Franzininho/badge-Aprenda-Soldar/img/02.jpg

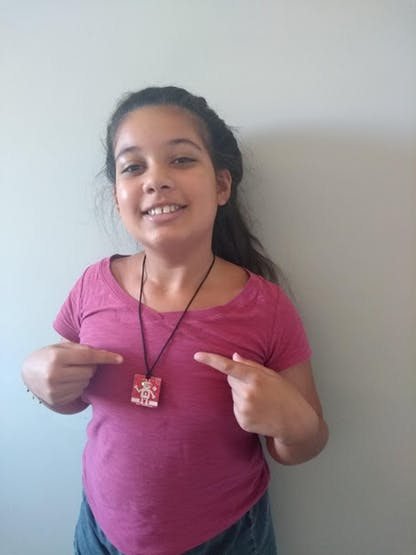
img/02.jpg
