Franzininho/badge-Aprenda-Soldar/img/01.jpg

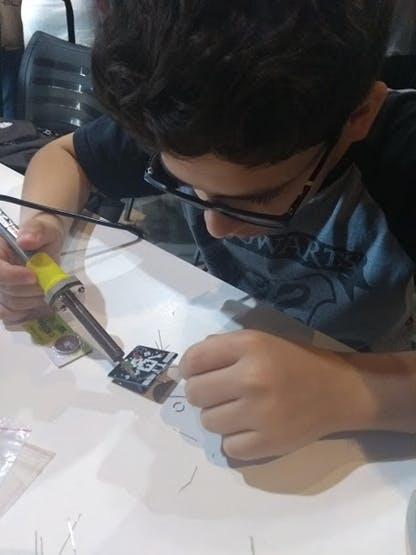
img/01.jpg
