Franzininho/badge-Aprenda-Soldar/img/03.jpg

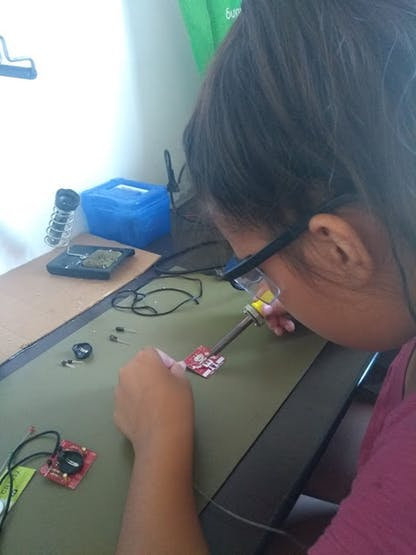
img/03.jpg
