Franzininho/badge-Aprenda-Soldar/img/04.jpg

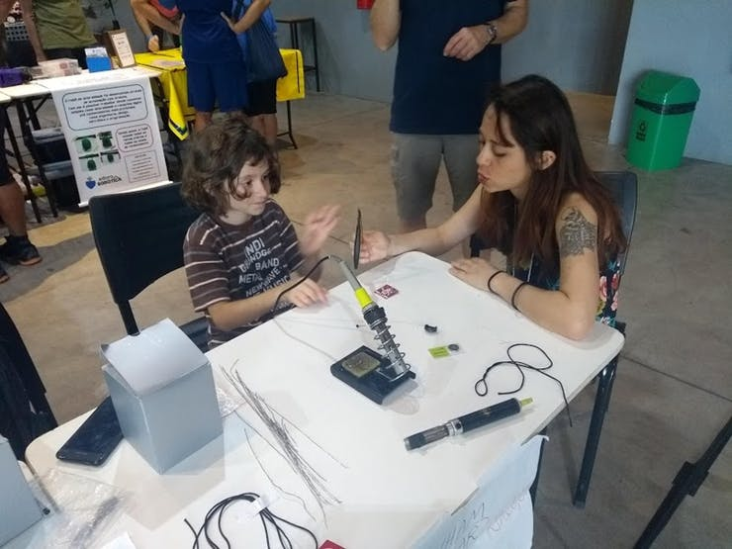
img/04.jpg
