Franzininho/badge-Aprenda-Soldar/img/06.jpg

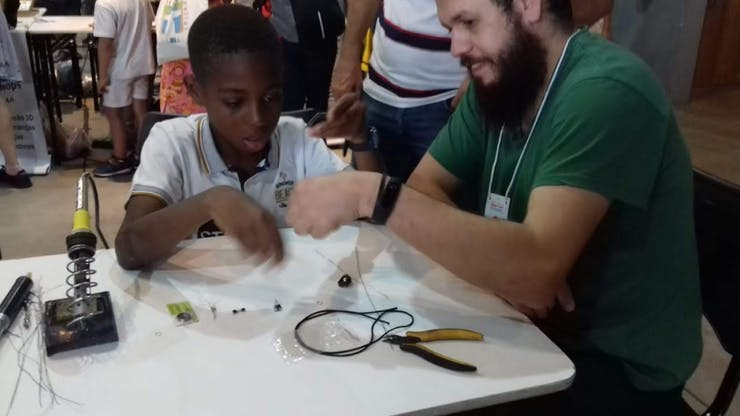
img/06.jpg
