Franzininho/badge-Aprenda-Soldar/img/07.jpeg

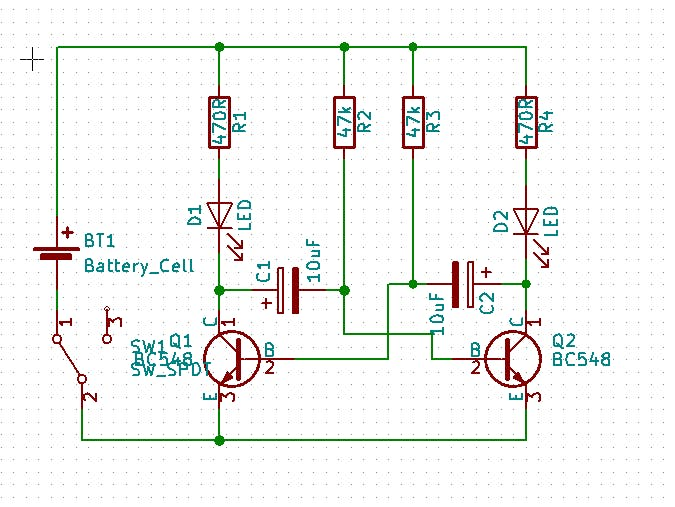
img/07.jpeg
