Franzininho/badge-Aprenda-Soldar/img/08.jpeg

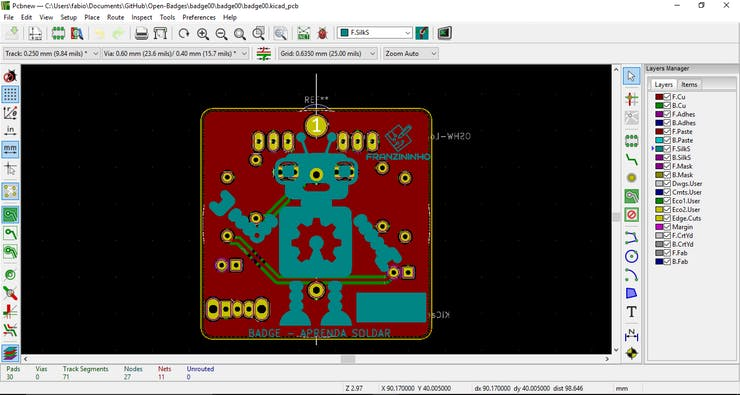
img/08.jpeg
