Franzininho/badge-Aprenda-Soldar/img/09.jpeg

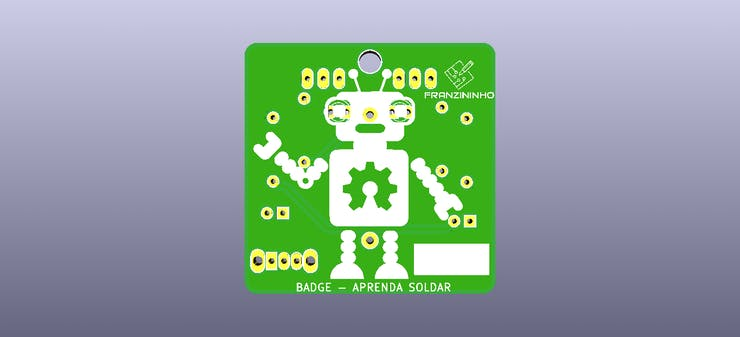
img/09.jpeg
