Franzininho/badge-Aprenda-Soldar/img/10.jpeg

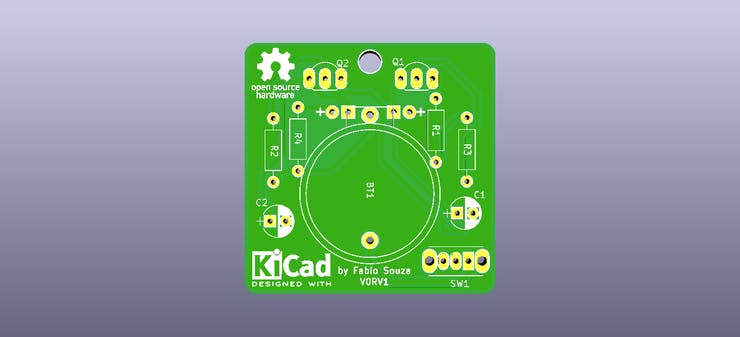
img/10.jpeg
