Franzininho/badge-Aprenda-Soldar/img/12.jpeg

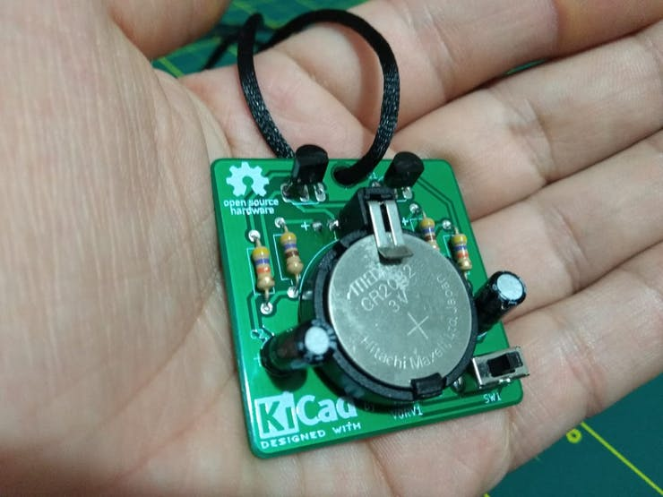
img/12.jpeg
