Franzininho/badge-Aprenda-Soldar/img/13.jpg

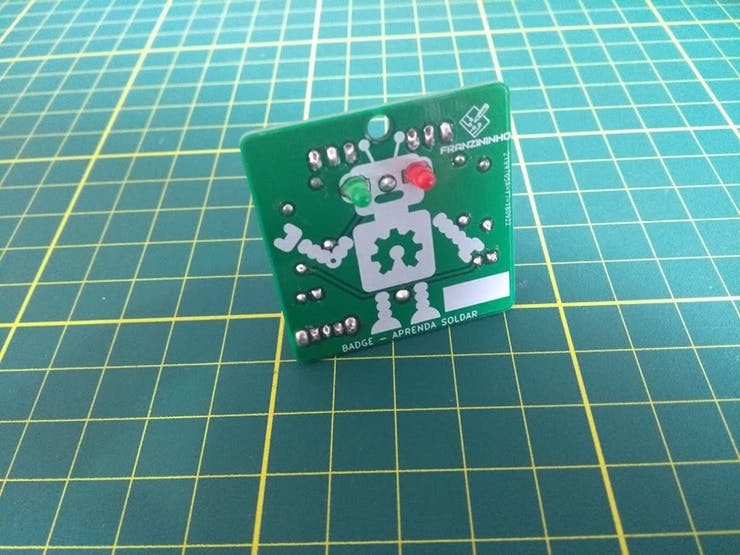
img/13.jpg
