Franzininho/badge-Aprenda-Soldar/img/14.jpeg

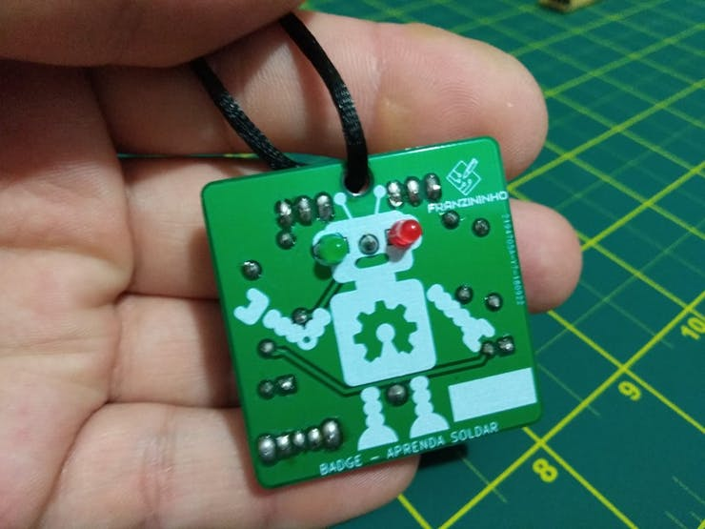
img/14.jpeg
