Franzininho/badge-Aprenda-Soldar/img/15.png

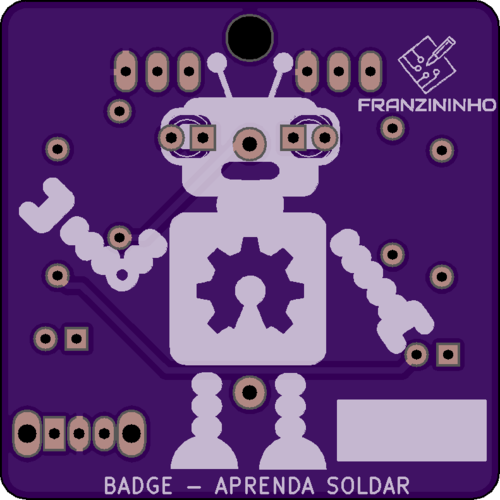
img/15.png
