Franzininho/badge-Aprenda-Soldar/img/16.png

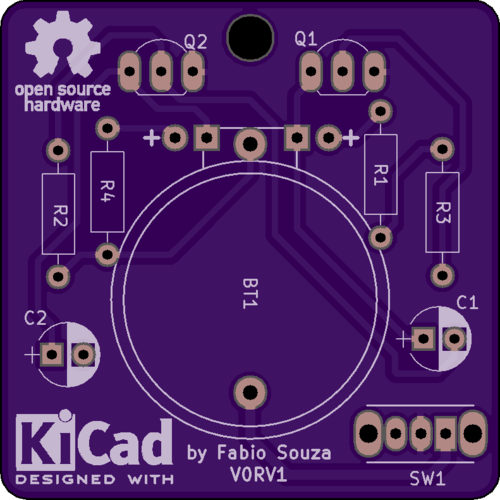
img/16.png
